fthouin/sound_conversion/Fab/coupes_barres.pdf

Inventaire

Description | Provenance | W | H | T | # dispo
Bar arrière longue | Assemblage C | 635 | 30 | 30 | 4
Bar longue côtés | Assemblage B | 1115 | 30 | 30 | 7
Barres courte côtés | Assemblage B | 260 | 30 | 30 | 8
barre longue coté endommagée | Assemblage B | 760 | 30 | 30 | 1
barres longue avant | Assemblage C | 635 | 30 | 30 | 5

Utilisé pour | Coupe | Utilisé
(brace_bar_back_panel_a,f), (brace_bar_back_panel_b,c) | W | 536.03
(brace_bar_back_panel_d,e) | W | 506.03
middle_brace_bar_fin_2 | W | 505.67
(side_panel_1_a,middle_brace_bar_fin_1and2_fin2) | W | 959.34
(side_panel_1_b,middle_brace_bar_fin_1and2_fin1) | W | 959.34
(side_panel_2_a, )(side_panel_2_b,) | W | 687
(middle_brace_bar_side_panel_2, brace_bar_fin_2_a) | W | 1106.86
(middle_brace_bar_side_panel_1, middle_brace_bar_fin_1) | W | 1063.67
side_panel_2_c, side_panel_1_c,d | Tel quel | 260
cross_brace_fin_1,2 | tel quel | 260
(middle_brace_bar_fin_1and_2_fin1,middle_brace_bar_fin_1and_2_fin2) w | 570.68
(front_panel_bar_a, driver_brace_bar_a) | w | 521.66
(front_panel_bar_b, driver_brace_bar_b) | w | 521.66
brace_bar_fin_1_a,b | w | 449.67
brace_bar_fin_2_b | W | 449.67

Nombre utilisé | Restant | L1 | L2
4 | 0
2 | 98.97 | 371.7 | 164.33
1 | 128.97 | 371.7 | 134.33
1 | 129.33 | 505.67
6 | 1
1 | 155.66 | 674 | 285.34
1 | 155.66 | 674 | 285.34
2 | 428 | 687
1 | 8.14 | 449.86 | 657
1 | 51.33 | 614 | 449.67
5 | 3
3 | 0 | 260
2 | 0 | 260
1 | 0
1 | 189.32 | 285.34 | 285.34
5 | 0
1 | 113.34 | 150 | 371.66
1 | 113.34 | 150 | 371.66
2 | 185.33 | 449.67
1 | 185.33 | 449.67
