fthouin/sound_conversion/Fab/coupes_panneaux.pdf

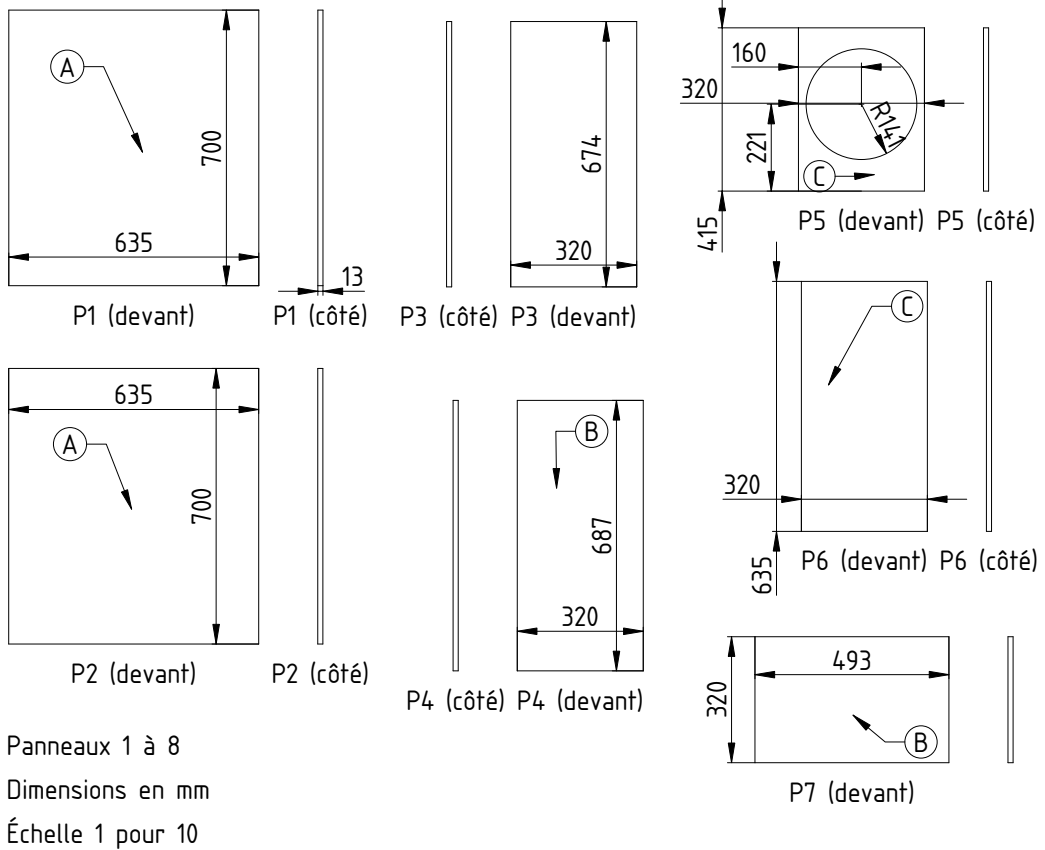
[picture p16: page 1]

635

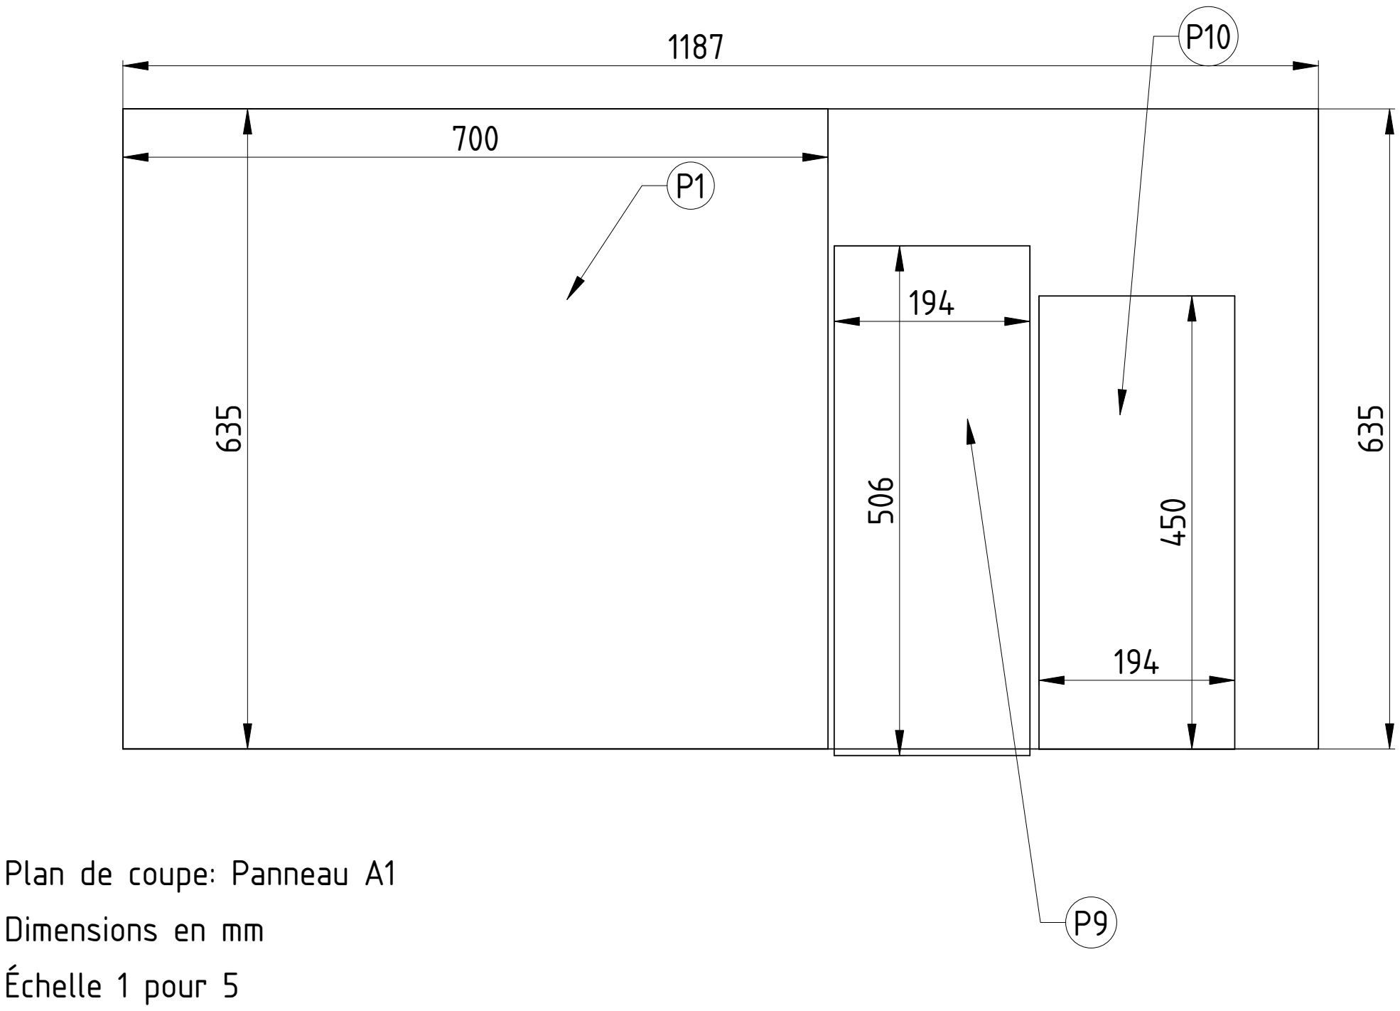
[picture p17: figure]
Plan de coupe: Panneau A1 Dimensions en mm Échelle 1 pour 5

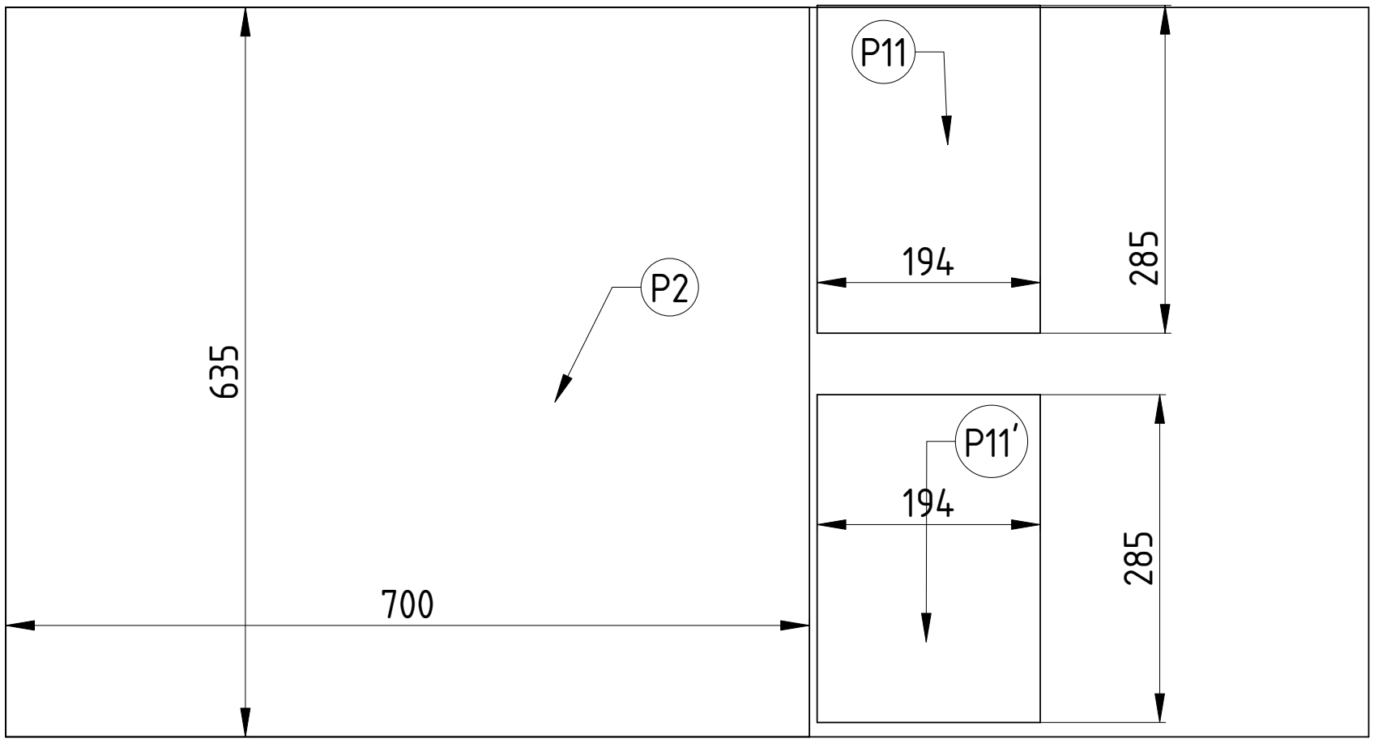
[picture p18: figure]

Plan de coupe: Panneau A2
Dimensions en mm

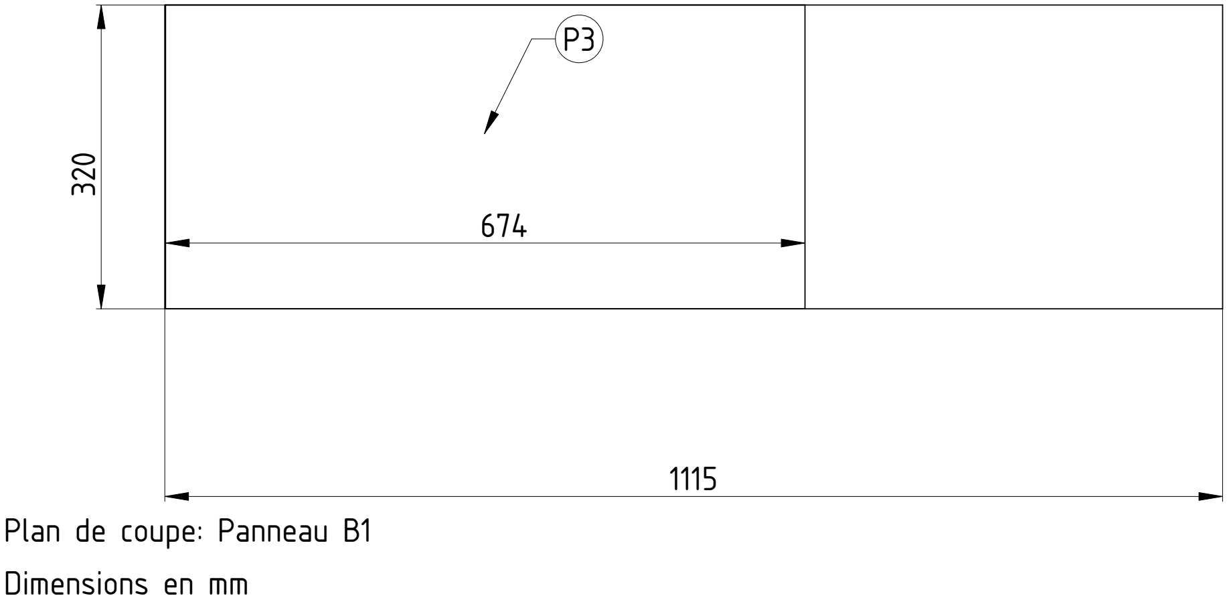
[picture p19: figure]
Plan de coupe: Panneau B1 Dimensions en mm

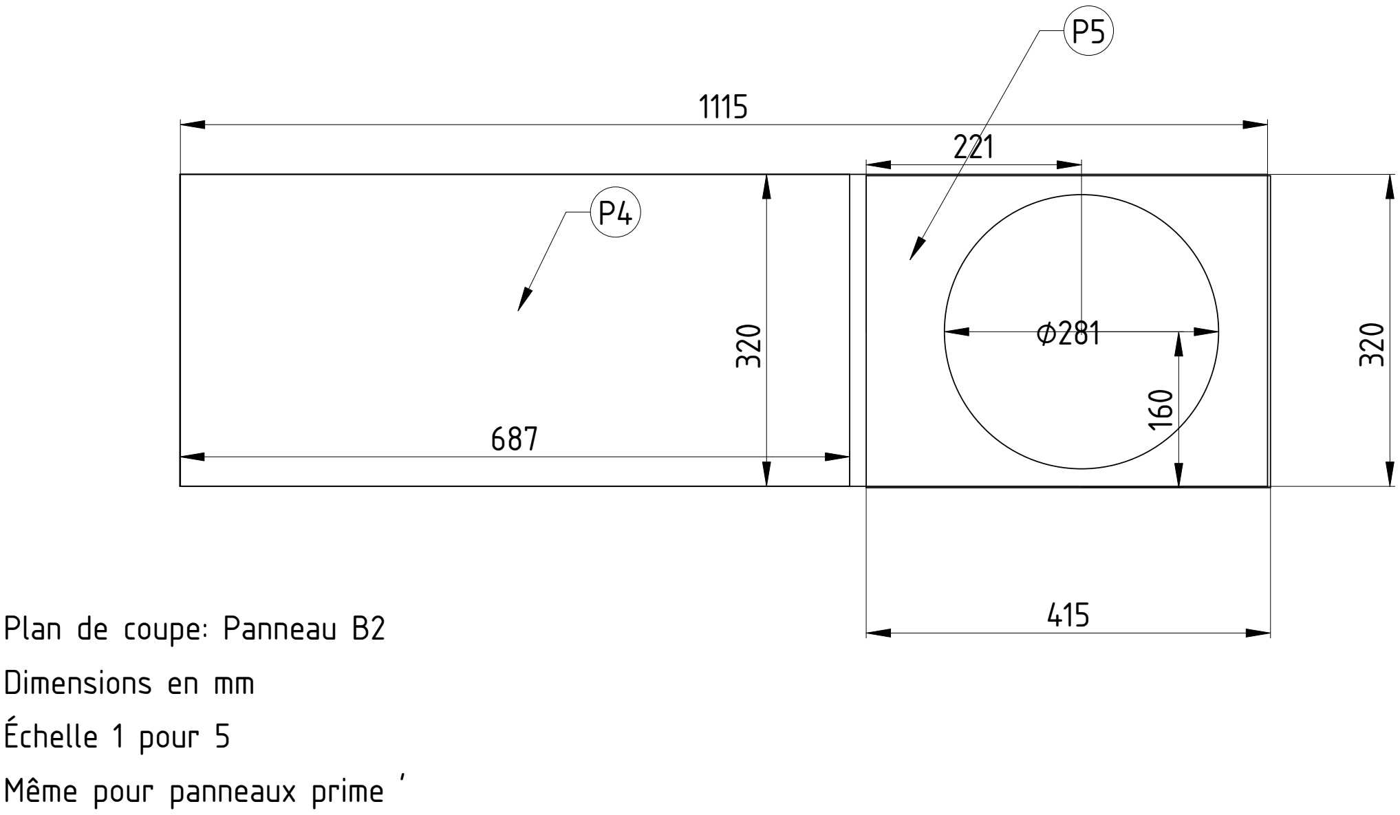
[picture p20: figure]
Plan de coupe: Panneau B2 Dimensions en mm Échelle 1 pour 5 Même pour panneaux prime '

P11 (devant)

2

8

5

194

P11 (côté)

13

P9 (devant)

5

0

6

194

P9 (côté)

P10 (côté)

13
P10 (devant)

194

4

5

0

Panneaux 8 à 11
Dimensions en mm
Échelle 1 pour 10

P8 (devant)

480

3

2

0

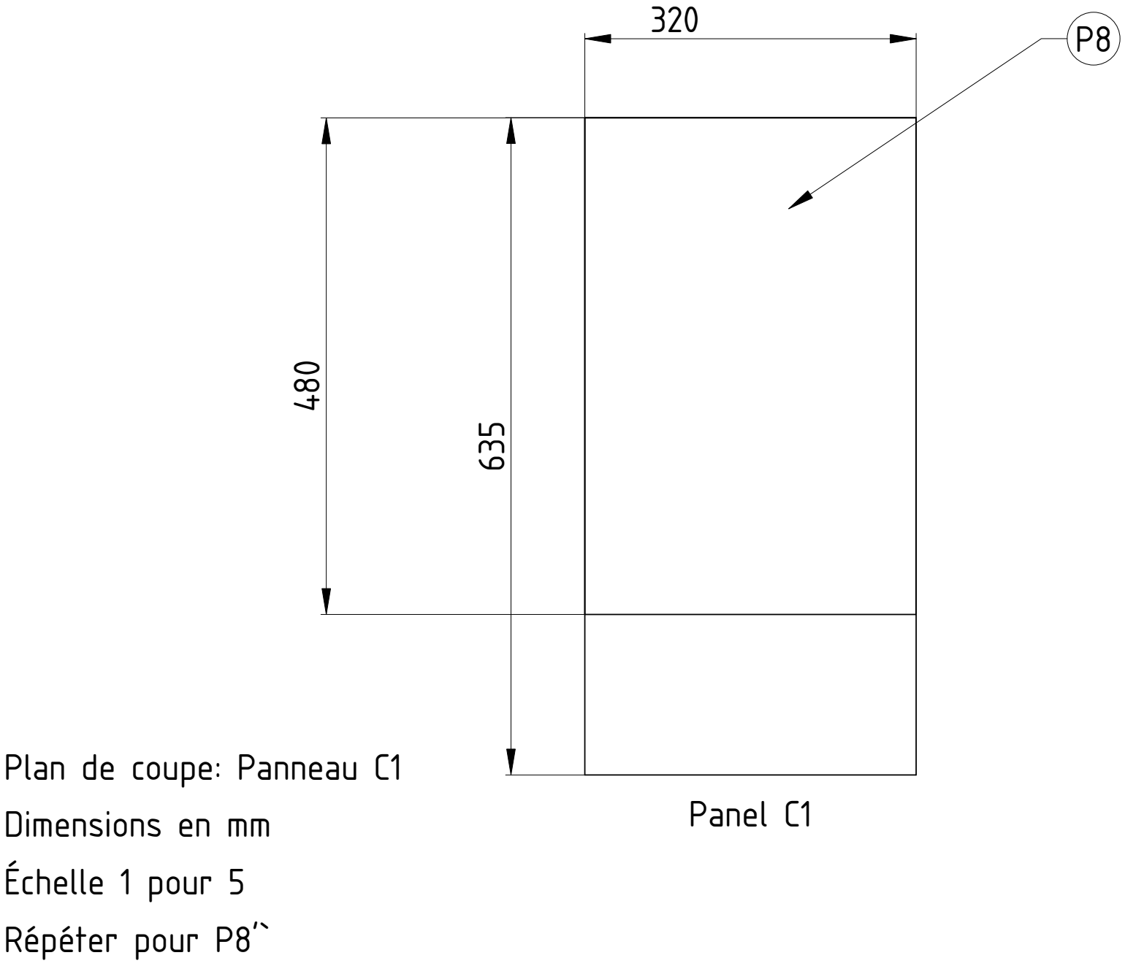
[picture p21: figure]
Panel C1; Plan de coupe: Panneau C1 Dimensions en mm Échelle 1 pour 5 Répéter pour P8'`

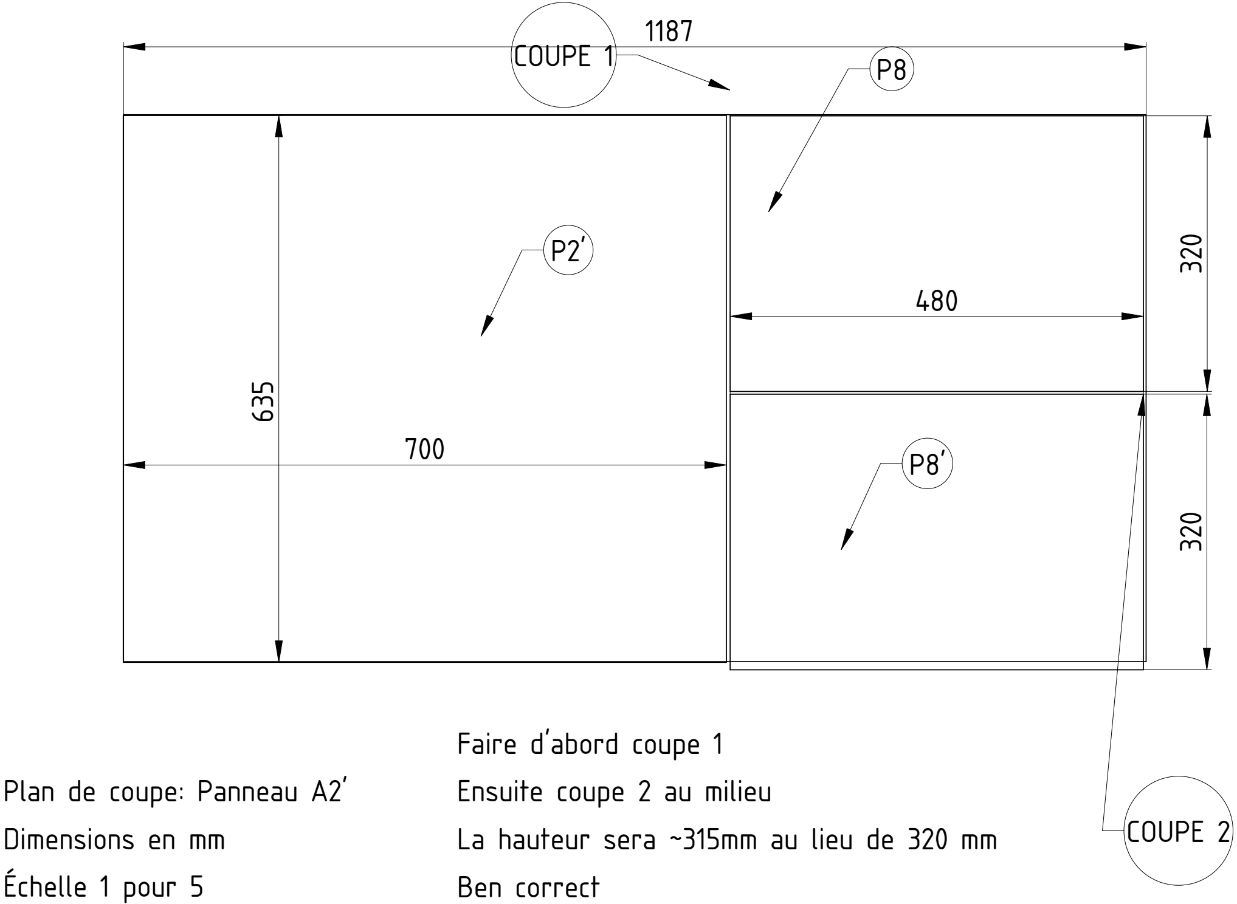
[picture p22: figure]
Plan de coupe: Panneau A2' Dimensions en mm; COUPE 1; Faire d'abord coupe 1 Ensuite coupe 2 au milieu; Ben correct; COUPE 2

La hauteur sera ~315mm au lieu de 320 mm
