fthouin/sound_conversion/Fab/assembly/side_panel_assembly_2.pdf

Assemblage: Side Panel 2
Dimensions en mm
Échelle 1 pour 5
Répéter pour prime
