fthouin/sound_conversion/Boxes/boite_lightcon_c231999.pdf

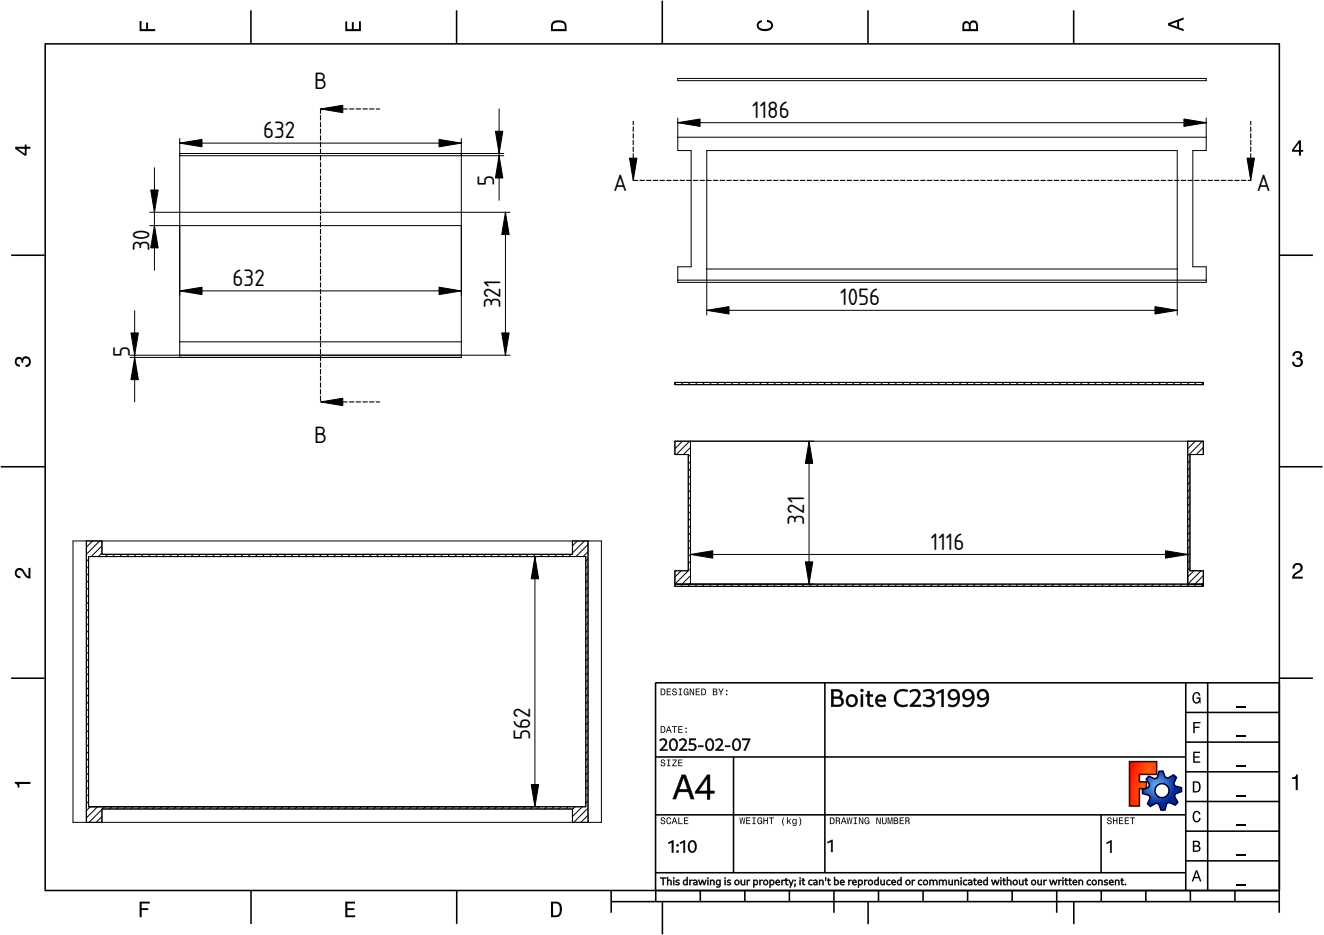
[picture p40: page 1]
